sonyxperiadev/CDB-Assist/Firmware-v3/CDBAssistNextGen.cydsn/adc.c

/*
 * adc.c - CDB Assist v3 voltage monitor handling
 *
 * Copyright (C) 2015-2016 Sony Mobile Communications Inc.
 * Author: Werner Johansson <werner.johansson@sonymobile.com>
 *
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
 * You should have received a copy of the GNU General Public License
 * along with this program.  If not, see <http://www.gnu.org/licenses/>.
 */

#include <project.h>
#include <stdio.h>
#include <string.h>
#include <stdint.h>

#include "adc.h"
#include "nv.h"

// Vtarget is considered valid if above 0.89V
#define VTARGETVALID (0.89f / 5.0f * 4096.0f)

int16_t adcvalues[ADCMAX] = { 0, 0, 0, 0, 0 };
int16_t adcavgvalues[ADCMAX] = { 0, 0, 0, 0, 0 };
int32_t adcavgaccum[ADCMAX] = { 0, 0, 0, 0, 0 };
uint16_t adcavgaccumcnt[ADCMAX] = { 0, 0, 0, 0, 0 };

// ADC_SAR_1 deals with Dummy load current and Target Vref voltages (ADC Vref=2.5V for 5V full-scale measurements)
// ADC_SAR_2 deals with VBAT, USB2VBUS and USB3VBUS voltages (ADC Vref=1.024V for 2.048V full-scale measurements)

CY_ISR( ADC_SAR_1_ISR ) {
    static uint8_t count = 0;
    static uint32_t accum = 0;
    static uint16_t hi = 0, lo = 0;
    int16_t adcval = CY_GET_REG16(ADC_SAR_1_SAR_WRK_PTR);
    count++;
    if((count & 0x7f) > 2) {
        accum += adcval;
        if(adcval > hi) hi = adcval;
        if(adcval < lo) lo = adcval;
    }
    if((count & 0x7f) > 19) {
        accum -= hi;
        accum -= lo;
        uint8_t adcidx = (count >> 7) + DUMMYLOAD;
        adcvalues[adcidx] = accum >> 4;
        adcavgaccum[adcidx] += accum >> 4;
        adcavgaccumcnt[adcidx]++;
        if(adcavgaccumcnt[adcidx] > 256) {
            adcavgvalues[adcidx] = adcavgaccum[adcidx] >> 8;
            adcavgaccum[adcidx] = 0;
            adcavgaccumcnt[adcidx] = 0;
        }
        accum = 0;
        hi = 0;
        lo = 0xffff;
        count ^= (1<<7);
        count &= 0x80;
        AMux_1_FastSelect(count >> 7);
    }
}

CY_ISR( ADC_SAR_2_ISR ) {
    static uint8_t count = 0;
    static uint8_t ch = 0;
    static uint32_t accum = 0;
    static uint16_t hi = 0, lo = 0;
    int16_t adcval = CY_GET_REG16(ADC_SAR_2_SAR_WRK_PTR);
    count++;
    if(count > 2) {
        accum += adcval;
        if(adcval > hi) hi = adcval;
        if(adcval < lo) lo = adcval;
    }
    if(count > 19) {
        accum -= hi;
        accum -= lo;
        adcvalues[ch] = accum >> 4;
        adcavgaccum[ch] += accum >> 4;
        adcavgaccumcnt[ch]++;
        if(adcavgaccumcnt[ch] > 256) {
            adcavgvalues[ch] = adcavgaccum[ch] >> 8;
            adcavgaccum[ch] = 0;
            adcavgaccumcnt[ch] = 0;
        }
        accum = 0;
        hi = 0;
        lo = 0xffff;
        ch++;
        if(ch > 2) ch = 0;
        count = 0;
        AMuxSeq_1_Next();
    }
}

float ADC_GetmVGain(int8_t gainadj) {
    float retval;
    // ADC readout * 22528mV / 4096 * gain adj
    retval = (22528.0f/4096.0f);
    retval *= (1 + ((float)(gainadj) * 0.001f)); // Adjust +/- 10% with a +/-100 adjust value    
    return retval;
}

float adcgain, adcgainvolt;

void ADC_CalcGain(void) {
    adcgain = ADC_GetmVGain( NVREAD->vbatvolt_adcgainadj );
    adcgainvolt = adcgain / 1000.0f;
}

void ADC_Init(void) {
    SenseRefGen_Start(); // Make sure we have our 2.5V ref which results in a 0-5V measurement range
    ADC_SAR_1_Start();
    AMux_1_Start();
    AMux_1_FastSelect(0);
    ADC_SAR_2_Start();
    AMuxSeq_1_Start();
    AMuxSeq_1_Next();
    ADC_SAR_1_IRQ_Enable();
    ADC_SAR_1_StartConvert();
    ADC_SAR_2_IRQ_Enable();
    ADC_SAR_2_StartConvert();
    ADC_CalcGain();
}

void ADC_Work( void ) {
//    for( uint8_t i=0; i<ADCMAX; i++ ) {
//        adcvalues[i] = ADC_SAR_Seq_1_GetResult16(i);
//    }
}

float ADC_GetVoltage( ADC_type sel ) {
    float retval = -1;
    if( sel < ADCMAX ) {
        float tmp = (float)adcavgvalues[sel];
        tmp += NVREAD->vbatvolt_adcoffsetadj;
        if( sel == VTARGETSENSE ) {
            tmp *= (5.0f / 4096.0f); // Convert to actual Volts
        } else {
            tmp *= adcgainvolt; // Convert to actual Volts
        }
        retval = tmp;
    }
    return retval;
}

uint16_t ADC_GetMillivolt( ADC_type sel ) {
    uint16_t retval = 0;
    if( sel < ADCMAX ) {
        float tmp = (float)adcavgvalues[sel];
        tmp += NVREAD->vbatvolt_adcoffsetadj;
        if( sel == VTARGETSENSE ) {
            tmp *= (5000.0f / 4096.0f);
        } else {
            tmp *= adcgain; // Convert to actual millivolts
        }
        retval = (uint16_t)tmp;
    }
    return retval;
}

uint16_t ADC_GetRaw( ADC_type sel ) {
    uint16_t retval = 0;
    if( sel < ADCMAX ) {
        retval = adcvalues[sel];
    }
    return retval;
}

uint16_t ADC_GetRawAvg( ADC_type sel ) {
    uint16_t retval = 0;
    if( sel < ADCMAX ) {
        retval = adcavgvalues[sel];
    }
    return retval;
}

uint8_t ADC_VtargetValid( void ) {
    return adcvalues[VTARGETSENSE] > VTARGETVALID;
}
