sonyxperiadev/CDB-Assist/Firmware-v3/CDBAssistNextGen.cydsn/bigfont.h

/*
 * bigfont.h - 12x16 font
 *
 * Copyright (C) 2010 Werner Johansson, wj@unifiedengineering.se
 *
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
 * You should have received a copy of the GNU General Public License
 * along with this program.  If not, see <http://www.gnu.org/licenses/>.
 */

#ifndef BIGFONT_H
#define BIGFONT_H

const uint16_t bigfont[] ={
0x0000,0x0000,0x0000,0x0000,0x0000,0x0000,0x0000,0x0000,0x0000,0x0000,0x0000,0x0000,
0x0000,0x0000,0x0000,0x0000,0x003c,0x1bfe,0x1bfe,0x003c,0x0000,0x0000,0x0000,0x0000,
0x0000,0x0000,0x0000,0x000e,0x000e,0x0000,0x0000,0x000e,0x000e,0x0000,0x0000,0x0000,
0x0000,0x0630,0x0630,0x1ffc,0x1ffc,0x0630,0x0630,0x1ffc,0x1ffc,0x0630,0x0630,0x0000,
0x0000,0x0438,0x0c7c,0x0ccc,0x0ccc,0x1ffe,0x1ffe,0x0ccc,0x0ccc,0x0f88,0x0700,0x0000,
0x0000,0x1c0e,0x0e0e,0x070e,0x0380,0x01c0,0x00e0,0x0070,0x1c38,0x1c1c,0x1c0e,0x0000,
0x0000,0x0638,0x0f7c,0x1fee,0x19c6,0x1dc6,0x0fe6,0x0f76,0x0e3e,0x1f1c,0x1b80,0x0000,
0x0000,0x0000,0x0000,0x0000,0x0000,0x0000,0x0008,0x000e,0x0006,0x0000,0x0000,0x0000,
0x0000,0x0000,0x0000,0x0000,0x07f8,0x0ffc,0x1c0e,0x1806,0x1806,0x0000,0x0000,0x0000,
0x0000,0x0000,0x0000,0x1806,0x1806,0x1c0e,0x0ffc,0x07f8,0x0000,0x0000,0x0000,0x0000,
0x0000,0x0000,0x0ccc,0x0edc,0x03f0,0x0ffc,0x0ffc,0x03f0,0x0edc,0x0ccc,0x0000,0x0000,
0x0000,0x0000,0x00c0,0x00c0,0x00c0,0x07f8,0x07f8,0x00c0,0x00c0,0x00c0,0x0000,0x0000,
0x0000,0x0000,0x0000,0x0000,0x2000,0x3800,0x1800,0x0000,0x0000,0x0000,0x0000,0x0000,
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
0x0000,0x0000,0x0000,0x0000,0x0000,0x0000,0x0000,0x0000,0x0000,0x0000,0x0000,0x0000,
0x0000,0x0000,0x0000,0x0000,0x0000,0x0000,0x0000,0x0000,0x0000,0x0000,0x0000,0x0000,
0x0000,0x0000,0x0000,0x0000,0x0000,0x0000,0x0000,0x0000,0x0000,0x0000,0x0000,0x0000};

#endif
