sonyxperiadev/CDB-Assist/Firmware-v3/CDBAssistNextGen.cydsn/dummyload.c

/*
 * dummyload.c - Dummy load handling
 *
 * Copyright (C) 2015-2016 Sony Mobile Communications Inc.
 * Author: Werner Johansson <werner.johansson@sonymobile.com>
 *
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
 * You should have received a copy of the GNU General Public License
 * along with this program.  If not, see <http://www.gnu.org/licenses/>.
 */

#include <project.h>
#include <stdint.h>
#include <stdio.h>
#include "dummyload.h"
#include "i2c.h"
#include "adc.h"
#include "nv.h"

uint16_t dummyload_minvolt;
float dummyload_cur,dummyload_temp;
uint8_t dummyload_maxdac,dummyload_curdac;
float dummyload_dacgain;
float dummyload_adcgain;
int8_t dummyload_dacoffset;

float DummyLoad_DAC_GetGain(int8_t gainadj) {
    float retval;
    // With a 68R resistor to ground from the CurSet pin the gain should have
    // been divided by 2785(mA) full-scale, but due to the internal resistance
    // in the ANAIF_RT_DAC3_SW3 switch connecting the pin to the bus the value
    // is much higher (resistance in the switch is around 50R, so 68R+50R
    // gives 2.048mA * (68R+50R) / 50mR sense resistor ~ 4833)
    retval = (256.0f*64.0f/4833.28f);
    retval *= (1 + ((float)(gainadj) * 0.001f)); // Adjust +/- 10% with a +/-100 adjust value
    return retval;
}

float DummyLoad_ADC_GetGain(int8_t gainadj) {
    float retval;
    // ADC readout * 5000mV / 4096 / (50mOhm * 32 PGA gain), result in mA * gain adj
    // Main sources of error here are the PGA gain and sense resistor accuracy
    retval = ((5000.0f/4096.0f)/(0.050f * 32));
    retval *= (1 + ((float)(gainadj) * 0.001f)); // Adjust +/- 10% with a +/-100 adjust value    
    return retval;
}

void DummyLoad_CalcGain(uint8_t zerodac) {
    dummyload_dacgain = DummyLoad_DAC_GetGain( zerodac ? 0 : NVREAD->dummyload_dacgainadj );
    dummyload_adcgain = DummyLoad_ADC_GetGain( NVREAD->dummyload_adcgainadj );
    dummyload_dacoffset = zerodac ? 0 : NVREAD->dummyload_dacoffsetadj;
}

void DummyLoad_Init( void ) {
    IDAC8_1_Start();
    IDAC8_1_SetRange(IDAC8_1_RANGE_32uA);
    IDAC8_1_SetValue(0);
    DummyLoadDriver_Start();
    PGA_1_Start();
    
    dummyload_minvolt = 0;
    dummyload_maxdac = dummyload_curdac = 0;
    
    DummyLoad_CalcGain(0);
}

void DummyLoad_Setpoints(uint16_t minvolt, uint16_t maxcur) {
    dummyload_minvolt = minvolt + 10;
    
    float tmp = (float)maxcur;
    tmp *= dummyload_dacgain; // Apply cal gain here
    tmp += 0.5f; // Rounding
    int16_t dacval = (uint16_t)tmp;
    dacval += (int16_t)dummyload_dacoffset;
    if( dacval  < 0 ) dacval = 0;
    
    IDAC8_1_SetValue(0);

    if(dacval > 2047) {
        dacval += 32; // Rounding
        dacval >>= 6; // Divide by 64 and choose 2mA range
        IDAC8_1_SetRange(IDAC8_1_RANGE_2mA);
    } else if(dacval > 255) {
        dacval += 4; // Rounding
        dacval >>= 3; // Divide by 8 and choose 255uA range
        IDAC8_1_SetRange(IDAC8_1_RANGE_255uA);
    } else {
        IDAC8_1_SetRange(IDAC8_1_RANGE_32uA); // Lowest range
    }

    dummyload_curdac = dummyload_maxdac = (uint8_t)dacval;
    IDAC8_1_SetValue(dummyload_curdac);
}

void DummyLoad_Work(uint16_t actualvolt) {
    if(actualvolt<dummyload_minvolt) {
        if(dummyload_curdac>0) {
            dummyload_curdac--;
            IDAC8_1_SetValue(dummyload_curdac);
        }
    } else {
        if(dummyload_curdac<dummyload_maxdac) {
            dummyload_curdac++;
            IDAC8_1_SetValue(dummyload_curdac);
        }
    }
}

void DummyLoad_ADCWork(void) {
    int16_t tmp = ADC_GetRaw(DUMMYLOAD);
    tmp += (int16_t)(NVREAD->dummyload_adcoffsetadj);
    dummyload_cur = (float)tmp;
    dummyload_cur *= dummyload_adcgain;

    dummyload_temp = I2C_Get_Temperature();

    if(dummyload_temp > 60.0f) {
        CyPins_SetPin(FanEna_0);
    } else {
        CyPins_ClearPin(FanEna_0);
    }
}

float DummyLoad_GetCur(void) {
    return dummyload_cur;
}

float DummyLoad_GetTemp(void) {
    return dummyload_temp;
}
