sonyxperiadev/CDB-Assist/Firmware-v3/CDBAssistNextGen.cydsn/i2c.h

#ifndef I2C_H_
#define I2C_H_
    
#define I2CADDR_AD5241 (0x2c)
#define I2CADDR_LM75 (0x4f)
#define I2CADDR_ISL28023_VBAT (0x50)
#define I2CADDR_ISL28023_VBUS (0x54)

#define ISL28023_IOUT_CAL_GAIN (0x38)
#define ISL28023_CONFIG_ICHANNEL (0xd4)
#define ISL28023_CONFIG_VCHANNEL (0xd5)
#define ISL28023_READ_VSHUNT_OUT (0xd6)
#define ISL28023_READ_VOUT (0x8b)
#define ISL28023_READ_IOUT (0x8c)
#define ISL28023_READ_POUT (0x96)

float I2C_GetCurGain(int8_t gainadj);
void I2C_CalcGain(void);
void I2C_Init( void );
int16_t I2C_Get_VBUS_Volt( void );
float I2C_Get_VBUS_Cur( void );
int16_t I2C_Get_VBAT_Volt( void );
int16_t I2C_Get_VBAT_VoltAvg( void );
float I2C_Get_VBAT_CurAvg( void );
int16_t I2C_Get_VBAT_CurRaw( void );
int16_t I2C_Get_VBAT_CurRawAvg( void );
float I2C_Get_Temperature( void );
void I2C_Work( void );

#endif // I2C_H_
