sonyxperiadev/CDB-Assist/Firmware-v3/CDBAssistNextGen.cydsn/smallfont.h

/*
 * smallfont.h - 6x6 uppercase-only font
 *
 * Copyright (C) 2010,2014 Werner Johansson, wj@unifiedengineering.se
 *
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
 * You should have received a copy of the GNU General Public License
 * along with this program.  If not, see <http://www.gnu.org/licenses/>.
 */

#ifndef SMALLFONT_H
#define SMALLFONT_H

const uint8_t smallfont[] ={
0x00,0x00,0x00,0x00,0x00,0x00, 0x00,0x00,0x00,0x2e,0x00,0x00,
0x00,0x00,0x06,0x00,0x06,0x00, 0x00,0x14,0x3e,0x14,0x3e,0x14,
0x00,0x24,0x2a,0x6b,0x2a,0x12, 0x00,0x22,0x12,0x08,0x24,0x22,
0x00,0x10,0x2c,0x2a,0x14,0x28, 0x00,0x00,0x04,0x02,0x00,0x00,
0x00,0x00,0x1c,0x22,0x00,0x00, 0x00,0x00,0x22,0x1c,0x00,0x00,
0x00,0x2a,0x1c,0x08,0x1c,0x2a, 0x00,0x08,0x08,0x3e,0x08,0x08,
0x00,0x00,0x20,0x10,0x00,0x00, 0x00,0x08,0x08,0x08,0x08,0x08,
0x00,0x00,0x00,0x20,0x00,0x00, 0x00,0x20,0x10,0x08,0x04,0x02,

0x00,0x1c,0x32,0x2a,0x26,0x1c, 0x00,0x00,0x04,0x3e,0x00,0x00,
0x00,0x24,0x32,0x2a,0x2a,0x24, 0x00,0x22,0x2a,0x2a,0x2a,0x14,
0x00,0x0e,0x08,0x08,0x08,0x3e, 0x00,0x2e,0x2a,0x2a,0x2a,0x12,
0x00,0x18,0x2c,0x2a,0x2a,0x10, 0x00,0x02,0x22,0x12,0x0a,0x06,
0x00,0x14,0x2a,0x2a,0x2a,0x14, 0x00,0x04,0x2a,0x2a,0x2a,0x1c,
0x00,0x00,0x00,0x14,0x00,0x00, 0x00,0x00,0x20,0x14,0x00,0x00,
0x00,0x00,0x08,0x14,0x22,0x00, 0x00,0x14,0x14,0x14,0x14,0x14,
0x00,0x00,0x22,0x14,0x08,0x00, 0x00,0x04,0x02,0x2a,0x0a,0x04,

0x00,0x1c,0x22,0x2e,0x2e,0x0c, 0x00,0x3c,0x0a,0x0a,0x0a,0x3c,
0x00,0x3e,0x2a,0x2a,0x2a,0x14, 0x00,0x1c,0x22,0x22,0x22,0x14,
0x00,0x3e,0x22,0x22,0x22,0x1c, 0x00,0x3e,0x2a,0x2a,0x2a,0x22,
0x00,0x3e,0x0a,0x0a,0x02,0x02, 0x00,0x1c,0x2a,0x2a,0x2a,0x3a,
0x00,0x3e,0x08,0x08,0x08,0x3e, 0x00,0x22,0x22,0x3e,0x22,0x22,
0x00,0x10,0x20,0x20,0x20,0x1e, 0x00,0x3e,0x08,0x08,0x14,0x22,
0x00,0x3e,0x20,0x20,0x20,0x20, 0x00,0x3e,0x04,0x08,0x04,0x3e,
0x00,0x3e,0x04,0x08,0x10,0x3e, 0x00,0x1c,0x22,0x22,0x22,0x1c,

0x00,0x3e,0x0a,0x0a,0x0a,0x04, 0x00,0x1c,0x22,0x22,0x32,0x3c,
0x00,0x3e,0x0a,0x0a,0x1a,0x24, 0x00,0x24,0x2a,0x2a,0x2a,0x10,
0x00,0x02,0x02,0x3e,0x02,0x02, 0x00,0x1e,0x20,0x20,0x20,0x1e,
0x00,0x06,0x18,0x20,0x18,0x06, 0x00,0x3e,0x10,0x08,0x10,0x3e,
0x00,0x22,0x14,0x08,0x14,0x22, 0x00,0x02,0x04,0x38,0x04,0x02,
0x00,0x22,0x32,0x2a,0x26,0x22, 0x00,0x00,0x3e,0x22,0x22,0x00,
0x00,0x02,0x04,0x08,0x10,0x20, 0x00,0x00,0x22,0x22,0x3e,0x00,
0x00,0x08,0x04,0x02,0x04,0x08, 0x00,0x20,0x20,0x20,0x20,0x20,

0x00,0x02,0x00,0x1c,0x22,0x22, // Degrees Celsius symbol at 0x80 (`)
};

#endif
